orgua/ettus_research_usrp_b205mini_case/pictures/DSC06548.jpg

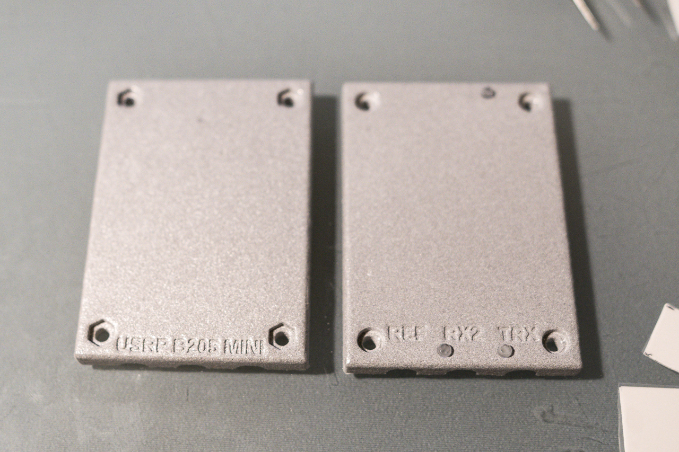
pictures/DSC06548.jpg
