orgua/ettus_research_usrp_b205mini_case/pictures/DSC06549.jpg

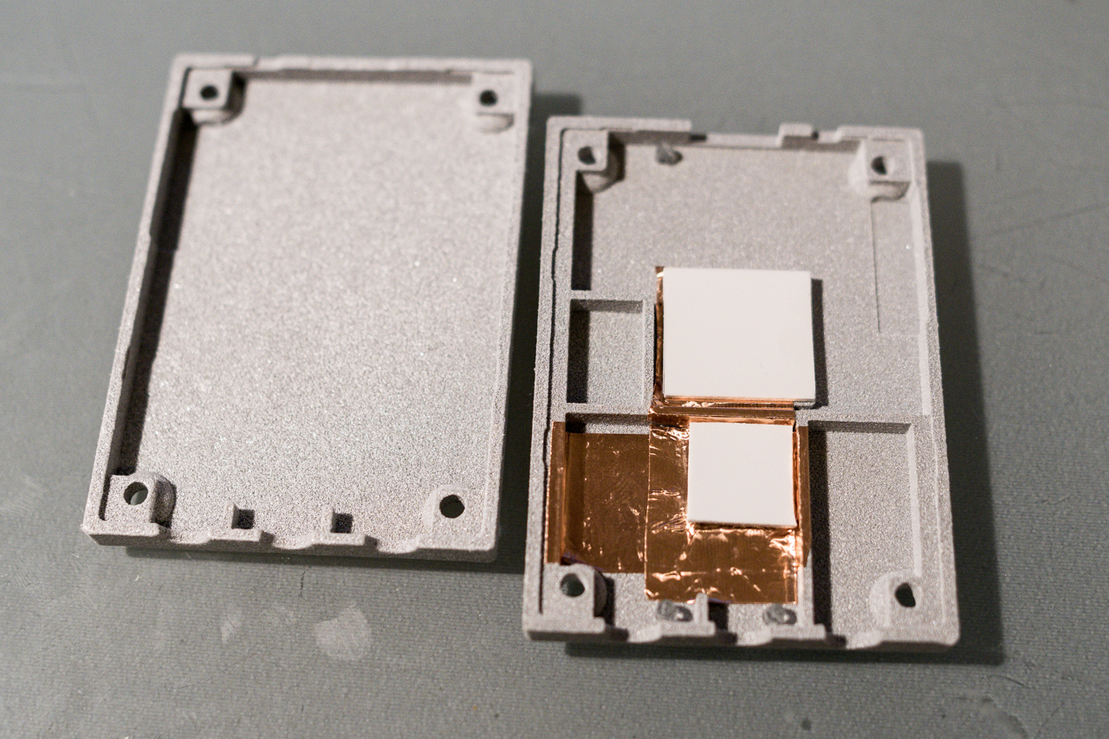
pictures/DSC06549.jpg
